JDesaulosSplunk/Splunk-O-Things/Schematics:Diagrams/Fritzing Files/SPLUNK IOT Prototype_etch_silk_bottom.pdf

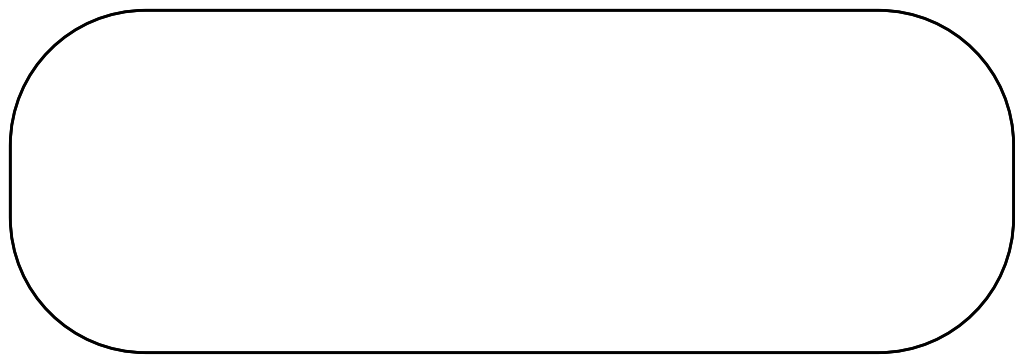
[picture p11: page 1]
