JDesaulosSplunk/Splunk-O-Things/Schematics:Diagrams/Fritzing Files/SPLUNK IOT Prototype_etch_silk_bottom_mirror.pdf

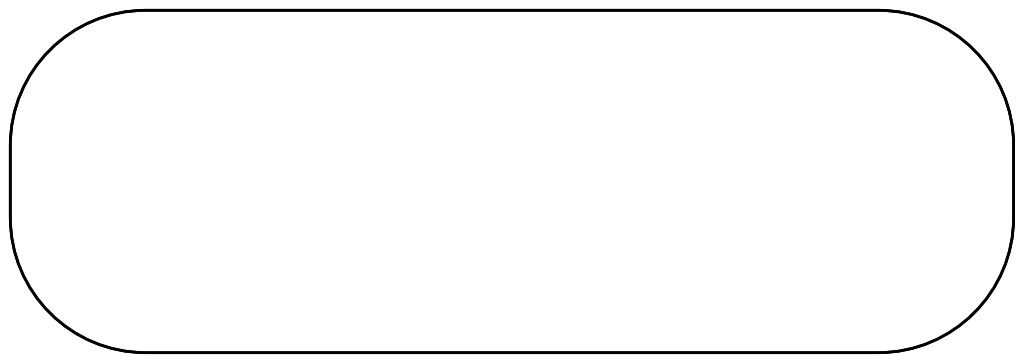
[picture p12: page 1]
