JDesaulosSplunk/Splunk-O-Things/Schematics:Diagrams/Fritzing Files/SPLUNK IOT Prototype_etch_silk_top.pdf

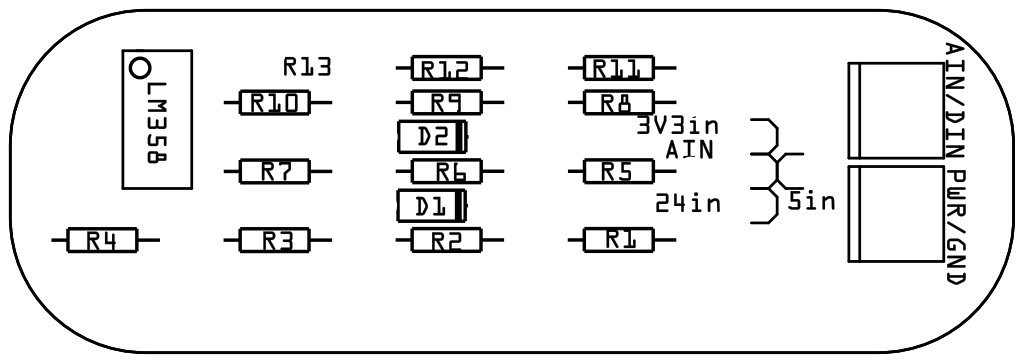
[picture p13: page 1]
