JDesaulosSplunk/Splunk-O-Things/Schematics:Diagrams/Fritzing Files/SPLUNK IOT Prototype_etch_silk_top_mirror.pdf

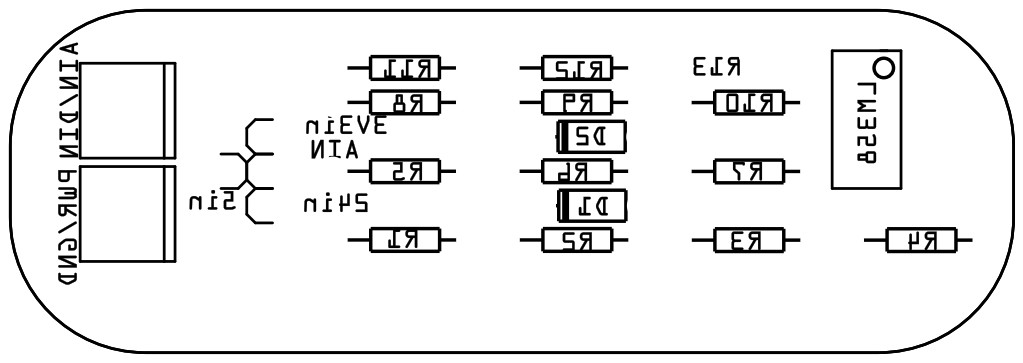
[picture p14: page 1]
